leighleighleigh/saab-93NG-bluetooth-aux/hardware/saab_bluetooth_aux_kit_v2/kicadlibrary/reference_images/lolin32_lite_bot.png

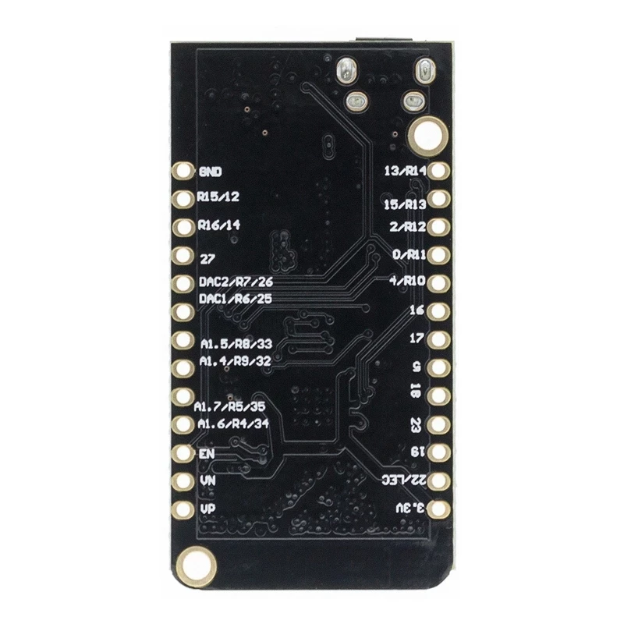
hardware/saab_bluetooth_aux_kit_v2/kicadlibrary/reference_images/lolin32_lite_bot.png
